cortexer/SCAR001_DC_LISN/02_RawPCB/DC_LISN-F.SilkS.pdf

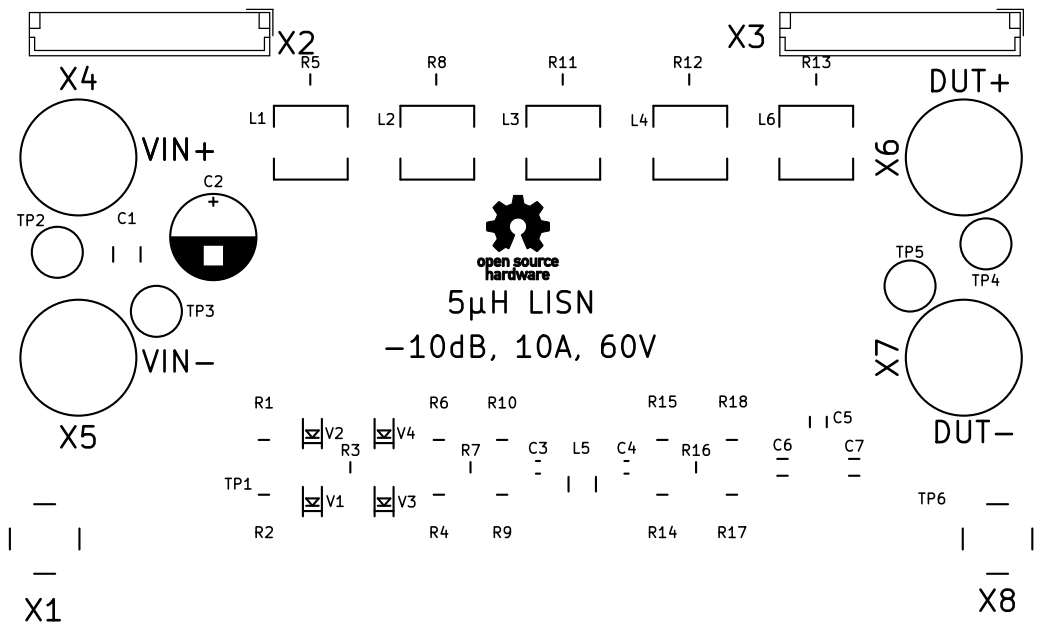
[picture p13: page 1]
