cortexer/SCAR001_DC_LISN/02_RawPCB/DC_LISN-In1.Cu.pdf

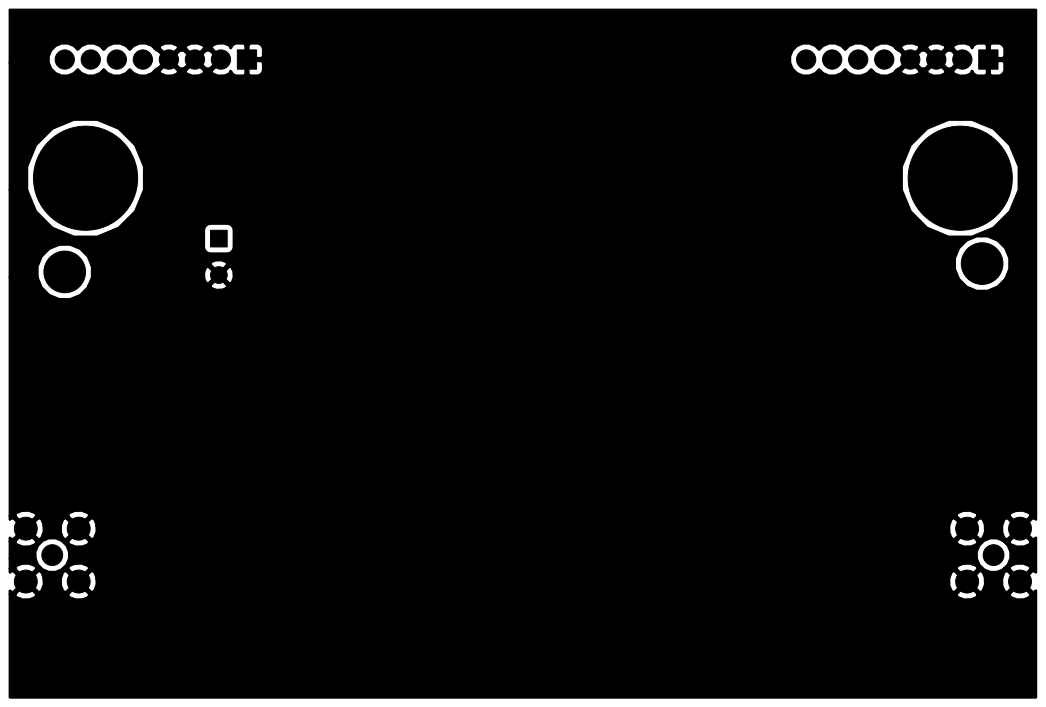
[picture p14: page 1]
