cortexer/SCAR001_DC_LISN/04_Simulations/DC2130A_LISN_TransferFunction.asc

C1: cap; 4.7µ
C2: cap; 22µ
C3: cap; 100n
C4: cap; 100n
C5: cap; 0.47µ
C6: cap; 0.47µ
D1: diode; 1N4148
D2: diode; 1N4148
D3: diode; 1N4148
D4: diode; 1N4148
L1: ind; 1.1µ
L2: ind; 1.1µ
L3: ind; 1.1µ
L4: ind; 1.1µ
L5: ind; 1.1µ
L6: ind; 1m
R1: res; 619
R2: res; 562
R3: res; 432
R4: res; 432
R5: res; 18.2
R6: res; 432
R7: res; 432
R8: res; 30.1
R9: res; 12.1
R10: res; 909
R11: res; 825
R12: res; 50
R13: res; 274
R14: res; 243
V1: voltage; 12
V2: voltage; ""; AC 1
Named nets: 0, SA, DUT+
.ac oct 100 1k 100Meg
DC2130A -10dB 5µH DC LISN
Spectrum Analyzer
The simulation shows the transfer function from the DUT terminals to the spectrum analyzer.
Therefore it shows the behaviour of the -10dB attenuator circuit.
The 50 ohm termination of the spectrum analyzer must be included in the model,
for the results being correct.
Parasitic component properties as well as layout effects have not been included
within this simulation.
DUT Terminals
