cortexer/SCAR001_DC_LISN/07_Measurements/Unit1/PNG3.png

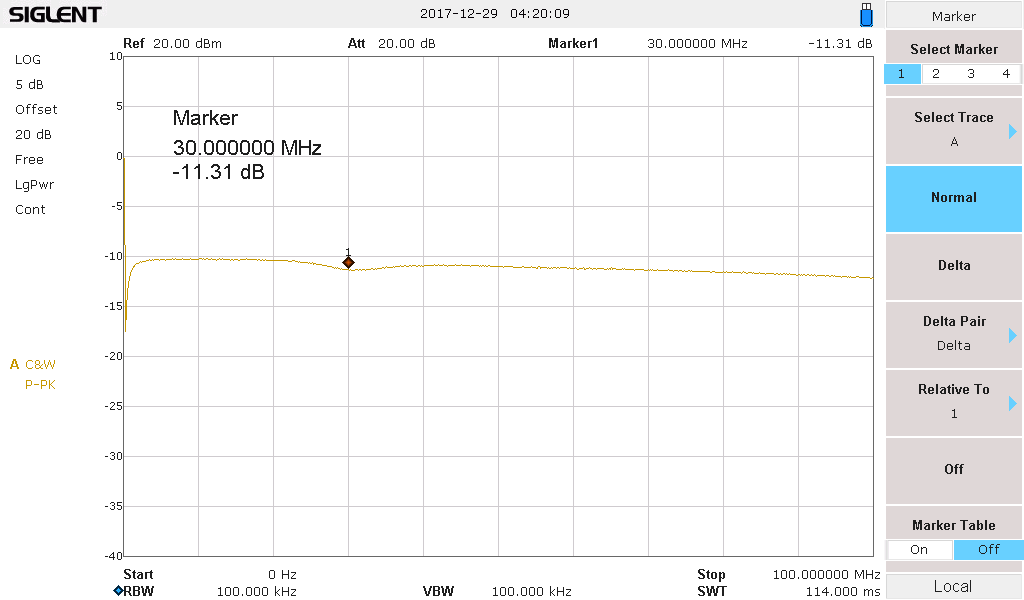
07_Measurements/Unit1/PNG3.png
