cortexer/SCAR001_DC_LISN/07_Measurements/Unit1/PNG5.png

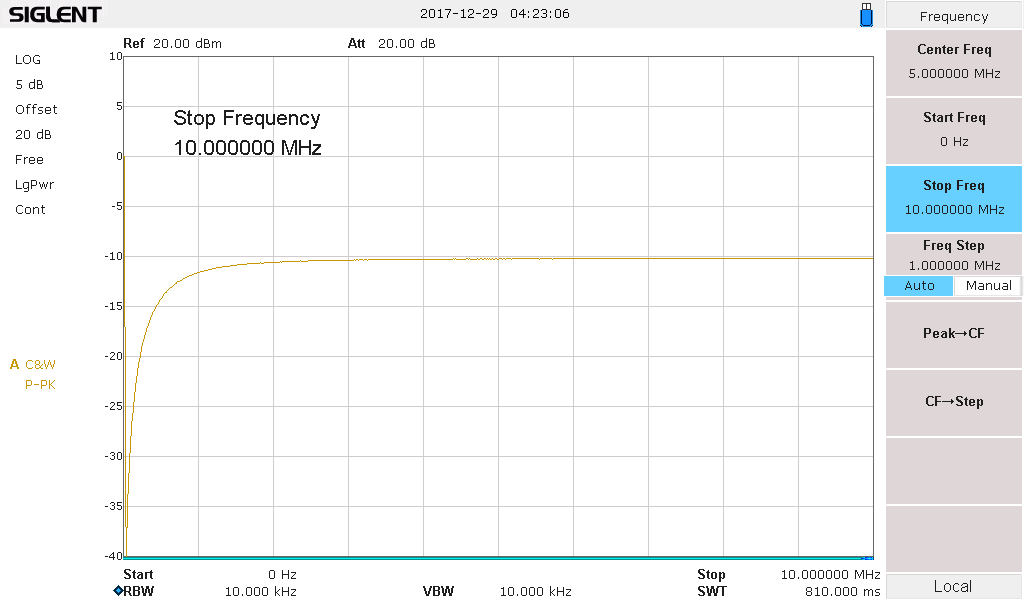
07_Measurements/Unit1/PNG5.png
